WARMW00D/HUD-Audi-A4-B9-MLB-Evo-Waveshare-ESP32-S3-Touch-LCD-3.49/waveshare_hud_mockup/hud_font_fuel.c

/*******************************************************************************
 * Size: 22 px
 * Bpp: 4
 * Opts: --font Montserrat-Bold-tnum.ttf --size 22 --bpp 4 --format lvgl --symbols 0123456789.Lлgal  -o hud_font_fuel.c --force-fast-kern-format --no-prefilter
 ******************************************************************************/

#define LV_LVGL_H_INCLUDE_SIMPLE
#ifdef LV_LVGL_H_INCLUDE_SIMPLE
#include "lvgl.h"
#else
#include "lvgl/lvgl.h"
#endif

#ifndef HUD_FONT_FUEL
#define HUD_FONT_FUEL 1
#endif

#if HUD_FONT_FUEL

/*-----------------
 *    BITMAPS
 *----------------*/

/*Store the image of the glyphs*/
static LV_ATTRIBUTE_LARGE_CONST const uint8_t glyph_bitmap[] = {
    /* U+0020 " " */

    /* U+002E "." */
    0x0, 0x19, 0x0, 0x57, 0xfe, 0x80, 0x3f, 0xfc,
    0x5, 0xff, 0x70, 0x1, 0xff, 0x90, 0x0,

    /* U+0030 "0" */
    0x0, 0xc7, 0x5d, 0xfe, 0xc6, 0x0, 0xfa, 0x3f,
    0xfe, 0xd2, 0x0, 0xd1, 0xff, 0xfd, 0xa0, 0x11,
    0x7f, 0xdc, 0x80, 0x55, 0xff, 0x40, 0x2, 0x3f,
    0xe3, 0x0, 0xdb, 0xfe, 0xe0, 0x6, 0xff, 0xb4,
    0x3, 0x9b, 0xfe, 0x30, 0xff, 0xa8, 0x3, 0x93,
    0xfe, 0x50, 0xff, 0xa4, 0x3, 0x8f, 0xfe, 0x60,
    0xff, 0xa8, 0x3, 0x93, 0xfe, 0x50, 0xdf, 0xf6,
    0x80, 0x73, 0x7f, 0xc6, 0x11, 0xff, 0x18, 0x6,
    0xdf, 0xf7, 0x0, 0xb, 0xfe, 0xe4, 0x2, 0xaf,
    0xfa, 0x0, 0x28, 0xff, 0xfe, 0xd0, 0xe, 0x8f,
    0xff, 0xb4, 0x80, 0x3c, 0x75, 0xdf, 0xec, 0x60,
    0xc,

    /* U+0031 "1" */
    0xd, 0xff, 0xf0, 0x80, 0x6d, 0xff, 0xf0, 0x80,
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
    0xff, 0x40, 0x4, 0xff, 0xf0, 0xf, 0x7f, 0x94,
    0x2, 0x7f, 0xfa, 0x7f, 0xf0, 0x80, 0x4f, 0xff,
    0x67, 0xfd, 0x20, 0x19, 0xff, 0xec, 0xff, 0x48,
    0x7, 0x3f, 0xfc
};


/*---------------------
 *  GLYPH DESCRIPTION
 *--------------------*/

static const lv_font_fmt_txt_glyph_dsc_t glyph_dsc[] = {
    {.bitmap_index = 0, .adv_w = 0, .box_w = 0, .box_h = 0, .ofs_x = 0, .ofs_y = 0} /* id = 0 reserved */,
    {.bitmap_index = 0, .adv_w = 100, .box_w = 0, .box_h = 0, .ofs_x = 0, .ofs_y = 0},
    {.bitmap_index = 0, .adv_w = 92, .box_w = 6, .box_h = 5, .ofs_x = 0, .ofs_y = 0},
    {.bitmap_index = 15, .adv_w = 246, .box_w = 15, .box_h = 15, .ofs_x = 0, .ofs_y = 0},
    {.bitmap_index = 104, .adv_w = 246, .box_w = 12, .box_h = 15, .ofs_x = 2, .ofs_y = 0},
    {.bitmap_index = 166, .adv_w = 246, .box_w = 14, .box_h = 15, .ofs_x = 0, .ofs_y = 0},
    {.bitmap_index = 237, .adv_w = 246, .box_w = 13, .box_h = 15, .ofs_x = 1, .ofs_y = 0},
    {.bitmap_index = 305, .adv_w = 246, .box_w = 15, .box_h = 15, .ofs_x = 0, .ofs_y = 0},
    {.bitmap_index = 378, .adv_w = 246, .box_w = 13, .box_h = 15, .ofs_x = 1, .ofs_y = 0},
    {.bitmap_index = 448, .adv_w = 246, .box_w = 14, .box_h = 15, .ofs_x = 1, .ofs_y = 0},
    {.bitmap_index = 534, .adv_w = 246, .box_w = 14, .box_h = 15, .ofs_x = 1, .ofs_y = 0},
    {.bitmap_index = 605, .adv_w = 246, .box_w = 14, .box_h = 15, .ofs_x = 1, .ofs_y = 0},
    {.bitmap_index = 692, .adv_w = 246, .box_w = 15, .box_h = 15, .ofs_x = 0, .ofs_y = 0},
    {.bitmap_index = 782, .adv_w = 213, .box_w = 13, .box_h = 15, .ofs_x = 1, .ofs_y = 0},
    {.bitmap_index = 843, .adv_w = 217, .box_w = 13, .box_h = 12, .ofs_x = 0, .ofs_y = 0},
    {.bitmap_index = 907, .adv_w = 246, .box_w = 14, .box_h = 16, .ofs_x = 0, .ofs_y = -4},
    {.bitmap_index = 1002, .adv_w = 106, .box_w = 5, .box_h = 17, .ofs_x = 1, .ofs_y = 0},
    {.bitmap_index = 1041, .adv_w = 234, .box_w = 13, .box_h = 12, .ofs_x = 0, .ofs_y = 0}
};

/*---------------------
 *  CHARACTER MAPPING
 *--------------------*/

static const uint16_t unicode_list_0[] = {
    0x0, 0xe, 0x10, 0x11, 0x12, 0x13, 0x14, 0x15,
    0x16, 0x17, 0x18, 0x19, 0x2c, 0x41, 0x47, 0x4c,
    0x41b
};

/*Collect the unicode lists and glyph_id offsets*/
static const lv_font_fmt_txt_cmap_t cmaps[] =
{
    {
        .range_start = 32, .range_length = 1052, .glyph_id_start = 1,
        .unicode_list = unicode_list_0, .glyph_id_ofs_list = NULL, .list_length = 17, .type = LV_FONT_FMT_TXT_CMAP_SPARSE_TINY
    }
};



/*--------------------
 *  ALL CUSTOM DATA
 *--------------------*/

#if LVGL_VERSION_MAJOR == 8
/*Store all the custom data of the font*/
static  lv_font_fmt_txt_glyph_cache_t cache;
#endif

#if LVGL_VERSION_MAJOR >= 8
static const lv_font_fmt_txt_dsc_t font_dsc = {
#else
static lv_font_fmt_txt_dsc_t font_dsc = {
#endif
    .glyph_bitmap = glyph_bitmap,
    .glyph_dsc = glyph_dsc,
    .cmaps = cmaps,
    .kern_dsc = NULL,
    .kern_scale = 0,
    .cmap_num = 1,
    .bpp = 4,
    .kern_classes = 0,
    .bitmap_format = 2,
#if LVGL_VERSION_MAJOR == 8
    .cache = &cache
#endif
};



/*-----------------
 *  PUBLIC FONT
 *----------------*/

/*Initialize a public general font descriptor*/
#if LVGL_VERSION_MAJOR >= 8
const lv_font_t hud_font_fuel = {
#else
lv_font_t hud_font_fuel = {
#endif
    .get_glyph_dsc = lv_font_get_glyph_dsc_fmt_txt,    /*Function pointer to get glyph's data*/
    .get_glyph_bitmap = lv_font_get_bitmap_fmt_txt,    /*Function pointer to get glyph's bitmap*/
    .line_height = 21,          /*The maximum line height required by the font*/
    .base_line = 4,             /*Baseline measured from the bottom of the line*/
#if !(LVGL_VERSION_MAJOR == 6 && LVGL_VERSION_MINOR == 0)
    .subpx = LV_FONT_SUBPX_NONE,
#endif
#if LV_VERSION_CHECK(7, 4, 0) || LVGL_VERSION_MAJOR >= 8
    .underline_position = -2,
    .underline_thickness = 1,
#endif
    .dsc = &font_dsc,          /*The custom font data. Will be accessed by `get_glyph_bitmap/dsc` */
#if LV_VERSION_CHECK(8, 2, 0) || LVGL_VERSION_MAJOR >= 9
    .fallback = NULL,
#endif
    .user_data = NULL,
};



#endif /*#if HUD_FONT_FUEL*/
