WARMW00D/HUD-Audi-A4-B9-MLB-Evo-Waveshare-ESP32-S3-Touch-LCD-3.49/waveshare_hud_mockup/hud_font_kmh.c

/*******************************************************************************
 * Size: 38 px
 * Bpp: 4
 * Opts: --font Montserrat-Bold-tnum.ttf --size 38 --bpp 4 --format lvgl --symbols km/hpкмч -o hud_font_kmh.c --force-fast-kern-format --no-prefilter
 ******************************************************************************/

#define LV_LVGL_H_INCLUDE_SIMPLE
#ifdef LV_LVGL_H_INCLUDE_SIMPLE
#include "lvgl.h"
#else
#include "lvgl/lvgl.h"
#endif

#ifndef HUD_FONT_KMH
#define HUD_FONT_KMH 1
#endif

#if HUD_FONT_KMH

/*-----------------
 *    BITMAPS
 *----------------*/

/*Store the image of the glyphs*/
static LV_ATTRIBUTE_LARGE_CONST const uint8_t glyph_bitmap[] = {
    /* U+002F "/" */
    0x0, 0xff, 0xe0, 0xf7, 0xfe, 0x60, 0xf, 0xfe,
    0x1, 0xff, 0xf0, 0x80, 0x7f, 0xf0, 0x27, 0xff,
    0x58, 0x7, 0xff, 0x7, 0xbf, 0xf2, 0x80, 0x7f,
    0xf0, 0x13, 0xff, 0x80, 0x3f, 0xf8, 0x35, 0xff,
    0xa8, 0x3, 0xff, 0x83, 0xff, 0xc8, 0x1, 0xff,
    0xc0, 0x5f, 0xfd, 0xc0, 0x1f, 0xfc, 0x1a, 0xff,
    0xd2, 0x1, 0xff, 0xc1, 0xff, 0xe4, 0x0, 0xff,
    0xe0, 0x2f, 0xfe, 0xe0, 0xf, 0xfe, 0xd, 0xff,
    0xe8, 0x0, 0xff, 0xe0, 0xf, 0xff, 0x18, 0x7,
    0xff, 0x1, 0xbf, 0xf6, 0x80, 0x7f, 0xf0, 0x73,
    0xff, 0x40, 0x7, 0xff, 0x0, 0x7f, 0xf8, 0x80,
    0x3f, 0xf8, 0xf, 0xff, 0xb4, 0x3, 0xff, 0x83,
    0xbf, 0xf9, 0xc0, 0x3f, 0xf8, 0x5, 0xff, 0xc4,
    0x1, 0xff, 0xc0, 0x8f, 0xfd, 0x80, 0x1f, 0xfc,
    0x1d, 0xff, 0xcc, 0x1, 0xff, 0xc0, 0x3f, 0xfe,
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
    0x8f, 0xff, 0x88, 0x2, 0x3f, 0xfe, 0x22, 0x7f,
    0xf1, 0x80, 0x6a, 0xff, 0xa0, 0x3, 0x1f, 0xff,
    0x11, 0x3f, 0xf8, 0xc0, 0x31, 0x7f, 0xb8, 0x3,
    0x8f, 0xff, 0x88, 0x9f, 0xfc, 0x60, 0x1f, 0xfc,
    0x13, 0xff, 0xe2, 0x27, 0xff, 0x18, 0x7, 0xff,
    0x4, 0xff, 0xf8, 0x80,

    /* U+0447 "ч" */
    0xcf, 0xfe, 0x30, 0xf, 0xaf, 0xff, 0x8f, 0x3f,
    0xf8, 0xc0, 0x3e, 0xbf, 0xfe, 0x3c, 0xff, 0xe3,
    0x0, 0xfa, 0xff, 0xf8, 0xf3, 0xff, 0x8c, 0x3,
    0xeb, 0xff, 0xe3, 0xcf, 0xfe, 0x30, 0xf, 0xaf,
    0xff, 0x8f, 0x3f, 0xf8, 0xc0, 0x3e, 0xbf, 0xfe,
    0x3c, 0xff, 0xe3, 0x0, 0xfa, 0xff, 0xf8, 0xef,
    0xff, 0x90, 0x3, 0xeb, 0xff, 0xe3, 0x9f, 0xfe,
    0xa0, 0xf, 0xaf, 0xff, 0x8d, 0xbf, 0xfd, 0x46,
    0x0, 0x25, 0xaf, 0xff, 0x18, 0xff, 0xff, 0xf1,
    0xcc, 0x27, 0xff, 0xff, 0x8c, 0x60, 0xb, 0xff,
    0xff, 0xe2, 0x98, 0x4, 0xfd, 0xff, 0xfa, 0xb3,
    0xff, 0x8c, 0x3, 0x91, 0xe6, 0x67, 0x40, 0x5,
    0xff, 0xf1, 0x80, 0x7f, 0xf0, 0xaf, 0xff, 0x8c,
    0x3, 0xff, 0x85, 0x7f, 0xfc, 0x60, 0x1f, 0xfc,
    0x2b, 0xff, 0xe3, 0x0, 0xff, 0xe1, 0x5f, 0xff,
    0x18, 0x7, 0xff, 0xa, 0xff, 0xf8, 0xc0, 0x3f,
    0xf8, 0x57, 0xff, 0xc6
};


/*---------------------
 *  GLYPH DESCRIPTION
 *--------------------*/

static const lv_font_fmt_txt_glyph_dsc_t glyph_dsc[] = {
    {.bitmap_index = 0, .adv_w = 0, .box_w = 0, .box_h = 0, .ofs_x = 0, .ofs_y = 0} /* id = 0 reserved */,
    {.bitmap_index = 0, .adv_w = 238, .box_w = 19, .box_h = 36, .ofs_x = -2, .ofs_y = -4},
    {.bitmap_index = 200, .adv_w = 420, .box_w = 22, .box_h = 29, .ofs_x = 2, .ofs_y = 0},
    {.bitmap_index = 389, .adv_w = 398, .box_w = 24, .box_h = 29, .ofs_x = 2, .ofs_y = 0},
    {.bitmap_index = 593, .adv_w = 638, .box_w = 36, .box_h = 21, .ofs_x = 2, .ofs_y = 0},
    {.bitmap_index = 818, .adv_w = 420, .box_w = 23, .box_h = 28, .ofs_x = 2, .ofs_y = -7},
    {.bitmap_index = 1005, .adv_w = 390, .box_w = 23, .box_h = 21, .ofs_x = 2, .ofs_y = 0},
    {.bitmap_index = 1161, .adv_w = 496, .box_w = 27, .box_h = 21, .ofs_x = 2, .ofs_y = 0},
    {.bitmap_index = 1349, .adv_w = 385, .box_w = 21, .box_h = 21, .ofs_x = 1, .ofs_y = 0}
};

/*---------------------
 *  CHARACTER MAPPING
 *--------------------*/

static const uint16_t unicode_list_0[] = {
    0x0, 0x39, 0x3c, 0x3e, 0x41, 0x40b, 0x40d, 0x418
};

/*Collect the unicode lists and glyph_id offsets*/
static const lv_font_fmt_txt_cmap_t cmaps[] =
{
    {
        .range_start = 47, .range_length = 1049, .glyph_id_start = 1,
        .unicode_list = unicode_list_0, .glyph_id_ofs_list = NULL, .list_length = 8, .type = LV_FONT_FMT_TXT_CMAP_SPARSE_TINY
    }
};



/*--------------------
 *  ALL CUSTOM DATA
 *--------------------*/

#if LVGL_VERSION_MAJOR == 8
/*Store all the custom data of the font*/
static  lv_font_fmt_txt_glyph_cache_t cache;
#endif

#if LVGL_VERSION_MAJOR >= 8
static const lv_font_fmt_txt_dsc_t font_dsc = {
#else
static lv_font_fmt_txt_dsc_t font_dsc = {
#endif
    .glyph_bitmap = glyph_bitmap,
    .glyph_dsc = glyph_dsc,
    .cmaps = cmaps,
    .kern_dsc = NULL,
    .kern_scale = 0,
    .cmap_num = 1,
    .bpp = 4,
    .kern_classes = 0,
    .bitmap_format = 2,
#if LVGL_VERSION_MAJOR == 8
    .cache = &cache
#endif
};



/*-----------------
 *  PUBLIC FONT
 *----------------*/

/*Initialize a public general font descriptor*/
#if LVGL_VERSION_MAJOR >= 8
const lv_font_t hud_font_kmh = {
#else
lv_font_t hud_font_kmh = {
#endif
    .get_glyph_dsc = lv_font_get_glyph_dsc_fmt_txt,    /*Function pointer to get glyph's data*/
    .get_glyph_bitmap = lv_font_get_bitmap_fmt_txt,    /*Function pointer to get glyph's bitmap*/
    .line_height = 39,          /*The maximum line height required by the font*/
    .base_line = 7,             /*Baseline measured from the bottom of the line*/
#if !(LVGL_VERSION_MAJOR == 6 && LVGL_VERSION_MINOR == 0)
    .subpx = LV_FONT_SUBPX_NONE,
#endif
#if LV_VERSION_CHECK(7, 4, 0) || LVGL_VERSION_MAJOR >= 8
    .underline_position = -4,
    .underline_thickness = 2,
#endif
    .dsc = &font_dsc,          /*The custom font data. Will be accessed by `get_glyph_bitmap/dsc` */
#if LV_VERSION_CHECK(8, 2, 0) || LVGL_VERSION_MAJOR >= 9
    .fallback = NULL,
#endif
    .user_data = NULL,
};



#endif /*#if HUD_FONT_KMH*/
