WARMW00D/HUD-Audi-A4-B9-MLB-Evo-Waveshare-ESP32-S3-Touch-LCD-3.49/waveshare_hud_mockup/hud_font_route.c

/*******************************************************************************
 * Size: 28 px
 * Bpp: 4
 * Opts: --font Montserrat-Bold-tnum.ttf --size 28 --bpp 4 --format lvgl --symbols 0123456789:.kmhift кмч -o hud_font_route.c --force-fast-kern-format --no-prefilter
 ******************************************************************************/

#define LV_LVGL_H_INCLUDE_SIMPLE
#ifdef LV_LVGL_H_INCLUDE_SIMPLE
#include "lvgl.h"
#else
#include "lvgl/lvgl.h"
#endif

#ifndef HUD_FONT_ROUTE
#define HUD_FONT_ROUTE 1
#endif

#if HUD_FONT_ROUTE

/*-----------------
 *    BITMAPS
 *----------------*/

/*Store the image of the glyphs*/
static LV_ATTRIBUTE_LARGE_CONST const uint8_t glyph_bitmap[] = {
    /* U+0020 " " */

    /* U+002E "." */
    0x0, 0xa, 0x18, 0x4, 0xbf, 0xf5, 0x0, 0x3b,
    0xff, 0x20, 0x7f, 0xf2, 0x86, 0x7f, 0xe2, 0x1,
    0xbf, 0xd5, 0x0,

    /* U+0030 "0" */
    0x0, 0xe6, 0xbe, 0xff, 0x6c, 0x98, 0x7, 0xe3,
    0xdf, 0xff, 0xd4, 0x20, 0x1c, 0x9f, 0xff, 0xf6,
    0x88, 0x4, 0x5f, 0xfe, 0xcd, 0xff, 0xea, 0x0,
    0xab, 0xff, 0x48, 0x4, 0x7b, 0xff, 0x90, 0x7,
    0xff, 0x60, 0x7, 0x17, 0xfe, 0xb0, 0x6f, 0xfc,
    0x80, 0x1e, 0xaf, 0xfc, 0x13, 0xff, 0x80, 0x3e,
    0x6f, 0xfc, 0x77, 0xff, 0x70, 0x7, 0xc9, 0xff,
    0x92, 0xff, 0xed, 0x0, 0xf9, 0x3f, 0xf2, 0xdf,
    0xfd, 0xc0, 0x1f, 0x27, 0xfe, 0x49, 0xff, 0xc0,
    0x1f, 0x37, 0xfe, 0x36, 0xff, 0xc8, 0x1, 0xea,
    0xff, 0xc0, 0x3f, 0xfb, 0x0, 0x38, 0xbf, 0xf5,
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
    0xeb, 0xef, 0xf8, 0x0, 0xbf, 0xfc, 0x40, 0x7f,
    0xf5, 0xf7, 0xfc, 0x1, 0x67, 0xfd, 0x0, 0x3,
    0xff, 0xaf, 0xbf, 0xe0, 0x8, 0xff, 0xdc, 0x1,
    0x1f, 0xfd, 0x7d, 0xff, 0x0, 0x66, 0x94, 0x0,
    0x8f, 0xfe, 0xbe, 0xff, 0x80, 0x3f, 0xc7, 0xff,
    0x60,

    /* U+0447 "ч" */
    0x1f, 0xfc, 0x80, 0x1d, 0x7f, 0xf5, 0xf, 0xfe,
    0x40, 0xe, 0xbf, 0xfa, 0x87, 0xff, 0x20, 0x7,
    0x5f, 0xfd, 0x43, 0xff, 0x90, 0x3, 0xaf, 0xfe,
    0xa1, 0xff, 0xc8, 0x1, 0xd7, 0xff, 0x50, 0x7f,
    0xe7, 0x0, 0xeb, 0xff, 0xa8, 0x3b, 0xff, 0x28,
    0x0, 0x9b, 0xbf, 0xea, 0x8, 0xff, 0xff, 0xe0,
    0xd0, 0xe, 0xff, 0xff, 0xf0, 0x28, 0x0, 0x33,
    0xff, 0xea, 0xdf, 0xfa, 0x80, 0x38, 0x91, 0x6,
    0x0, 0xbf, 0xfa, 0x80, 0x3f, 0xeb, 0xff, 0xa8,
    0x3, 0xfe, 0xbf, 0xfa, 0x80, 0x3f, 0xeb, 0xff,
    0xa8, 0x3, 0xfe, 0xbf, 0xfa, 0x80
};


/*---------------------
 *  GLYPH DESCRIPTION
 *--------------------*/

static const lv_font_fmt_txt_glyph_dsc_t glyph_dsc[] = {
    {.bitmap_index = 0, .adv_w = 0, .box_w = 0, .box_h = 0, .ofs_x = 0, .ofs_y = 0} /* id = 0 reserved */,
    {.bitmap_index = 0, .adv_w = 127, .box_w = 0, .box_h = 0, .ofs_x = 0, .ofs_y = 0},
    {.bitmap_index = 0, .adv_w = 117, .box_w = 7, .box_h = 6, .ofs_x = 0, .ofs_y = 0},
    {.bitmap_index = 19, .adv_w = 314, .box_w = 18, .box_h = 19, .ofs_x = 1, .ofs_y = 0},
    {.bitmap_index = 139, .adv_w = 314, .box_w = 14, .box_h = 19, .ofs_x = 3, .ofs_y = 0},
    {.bitmap_index = 222, .adv_w = 314, .box_w = 17, .box_h = 19, .ofs_x = 1, .ofs_y = 0},
    {.bitmap_index = 323, .adv_w = 314, .box_w = 17, .box_h = 19, .ofs_x = 1, .ofs_y = 0},
    {.bitmap_index = 427, .adv_w = 314, .box_w = 18, .box_h = 19, .ofs_x = 1, .ofs_y = 0},
    {.bitmap_index = 531, .adv_w = 314, .box_w = 17, .box_h = 19, .ofs_x = 1, .ofs_y = 0},
    {.bitmap_index = 638, .adv_w = 314, .box_w = 18, .box_h = 19, .ofs_x = 1, .ofs_y = 0},
    {.bitmap_index = 759, .adv_w = 314, .box_w = 18, .box_h = 19, .ofs_x = 1, .ofs_y = 0},
    {.bitmap_index = 863, .adv_w = 314, .box_w = 18, .box_h = 19, .ofs_x = 1, .ofs_y = 0},
    {.bitmap_index = 988, .adv_w = 314, .box_w = 18, .box_h = 19, .ofs_x = 1, .ofs_y = 0},
    {.bitmap_index = 1108, .adv_w = 117, .box_w = 7, .box_h = 15, .ofs_x = 0, .ofs_y = 0},
    {.bitmap_index = 1146, .adv_w = 173, .box_w = 12, .box_h = 21, .ofs_x = 0, .ofs_y = 0},
    {.bitmap_index = 1233, .adv_w = 310, .box_w = 16, .box_h = 21, .ofs_x = 2, .ofs_y = 0},
    {.bitmap_index = 1340, .adv_w = 135, .box_w = 6, .box_h = 22, .ofs_x = 1, .ofs_y = 0},
    {.bitmap_index = 1392, .adv_w = 293, .box_w = 17, .box_h = 21, .ofs_x = 2, .ofs_y = 0},
    {.bitmap_index = 1513, .adv_w = 470, .box_w = 26, .box_h = 15, .ofs_x = 2, .ofs_y = 0},
    {.bitmap_index = 1651, .adv_w = 195, .box_w = 12, .box_h = 19, .ofs_x = 0, .ofs_y = 0},
    {.bitmap_index = 1731, .adv_w = 288, .box_w = 16, .box_h = 15, .ofs_x = 2, .ofs_y = 0},
    {.bitmap_index = 1826, .adv_w = 365, .box_w = 19, .box_h = 15, .ofs_x = 2, .ofs_y = 0},
    {.bitmap_index = 1939, .adv_w = 284, .box_w = 16, .box_h = 15, .ofs_x = 0, .ofs_y = 0}
};

/*---------------------
 *  CHARACTER MAPPING
 *--------------------*/

static const uint16_t unicode_list_0[] = {
    0x0, 0xe, 0x10, 0x11, 0x12, 0x13, 0x14, 0x15,
    0x16, 0x17, 0x18, 0x19, 0x1a, 0x46, 0x48, 0x49,
    0x4b, 0x4d, 0x54, 0x41a, 0x41c, 0x427
};

/*Collect the unicode lists and glyph_id offsets*/
static const lv_font_fmt_txt_cmap_t cmaps[] =
{
    {
        .range_start = 32, .range_length = 1064, .glyph_id_start = 1,
        .unicode_list = unicode_list_0, .glyph_id_ofs_list = NULL, .list_length = 22, .type = LV_FONT_FMT_TXT_CMAP_SPARSE_TINY
    }
};



/*--------------------
 *  ALL CUSTOM DATA
 *--------------------*/

#if LVGL_VERSION_MAJOR == 8
/*Store all the custom data of the font*/
static  lv_font_fmt_txt_glyph_cache_t cache;
#endif

#if LVGL_VERSION_MAJOR >= 8
static const lv_font_fmt_txt_dsc_t font_dsc = {
#else
static lv_font_fmt_txt_dsc_t font_dsc = {
#endif
    .glyph_bitmap = glyph_bitmap,
    .glyph_dsc = glyph_dsc,
    .cmaps = cmaps,
    .kern_dsc = NULL,
    .kern_scale = 0,
    .cmap_num = 1,
    .bpp = 4,
    .kern_classes = 0,
    .bitmap_format = 2,
#if LVGL_VERSION_MAJOR == 8
    .cache = &cache
#endif
};



/*-----------------
 *  PUBLIC FONT
 *----------------*/

/*Initialize a public general font descriptor*/
#if LVGL_VERSION_MAJOR >= 8
const lv_font_t hud_font_route = {
#else
lv_font_t hud_font_route = {
#endif
    .get_glyph_dsc = lv_font_get_glyph_dsc_fmt_txt,    /*Function pointer to get glyph's data*/
    .get_glyph_bitmap = lv_font_get_bitmap_fmt_txt,    /*Function pointer to get glyph's bitmap*/
    .line_height = 22,          /*The maximum line height required by the font*/
    .base_line = 0,             /*Baseline measured from the bottom of the line*/
#if !(LVGL_VERSION_MAJOR == 6 && LVGL_VERSION_MINOR == 0)
    .subpx = LV_FONT_SUBPX_NONE,
#endif
#if LV_VERSION_CHECK(7, 4, 0) || LVGL_VERSION_MAJOR >= 8
    .underline_position = -3,
    .underline_thickness = 1,
#endif
    .dsc = &font_dsc,          /*The custom font data. Will be accessed by `get_glyph_bitmap/dsc` */
#if LV_VERSION_CHECK(8, 2, 0) || LVGL_VERSION_MAJOR >= 9
    .fallback = NULL,
#endif
    .user_data = NULL,
};



#endif /*#if HUD_FONT_ROUTE*/
