WARMW00D/HUD-Audi-A4-B9-MLB-Evo-Waveshare-ESP32-S3-Touch-LCD-3.49/waveshare_hud_mockup/hud_font_sign2.c

/*******************************************************************************
 * Size: 40 px
 * Bpp: 4
 * Opts: --font RobotoCondensed-Bold.ttf --size 40 --bpp 4 --format lvgl --symbols 0123456789 -o hud_font_sign2.c --force-fast-kern-format --no-prefilter
 ******************************************************************************/

#define LV_LVGL_H_INCLUDE_SIMPLE
#ifdef LV_LVGL_H_INCLUDE_SIMPLE
#include "lvgl.h"
#else
#include "lvgl/lvgl.h"
#endif

#ifndef HUD_FONT_SIGN2
#define HUD_FONT_SIGN2 1
#endif

#if HUD_FONT_SIGN2

/*-----------------
 *    BITMAPS
 *----------------*/

/*Store the image of the glyphs*/
static LV_ATTRIBUTE_LARGE_CONST const uint8_t glyph_bitmap[] = {
    /* U+0030 "0" */
    0x0, 0xe2, 0x9d, 0xff, 0x75, 0x20, 0x7, 0xf4,
    0x7f, 0xfe, 0xb0, 0xf, 0xa3, 0xff, 0xfd, 0x80,
    0x1c, 0x9f, 0xff, 0xfc, 0x7, 0x0, 0xd9, 0xff,
    0xd9, 0x7f, 0xfe, 0x10, 0x1, 0x7f, 0xf3, 0x80,
    0x13, 0xff, 0x98, 0x1, 0x1f, 0xfb, 0x80, 0x35,
    0xff, 0xeb, 0x0, 0x5f, 0xfe, 0xa0, 0xc, 0xff,
    0xfc, 0x0, 0xef, 0xfc, 0xe0, 0x19, 0x3f, 0xf8,
    0x83, 0xff, 0x98, 0x3, 0x17, 0xff, 0x18, 0xff,
    0xf2, 0x80, 0x62, 0xff, 0xe5, 0x2f, 0xfe, 0x50,
    0xc, 0x5f, 0xfc, 0xa5, 0xff, 0xca, 0x1, 0x8b,
    0xff, 0x94, 0xbf, 0xf9, 0x40, 0x31, 0x7f, 0xf2,
    0x97, 0xff, 0x28, 0x6, 0x2f, 0xfe, 0x52, 0xff,
    0xe5, 0x0, 0xc5, 0xff, 0xca, 0x5f, 0xfc, 0xa0,
    0x18, 0xbf, 0xf9, 0x4b, 0xff, 0x94, 0x3, 0x17,
    0xff, 0x28, 0xff, 0xf2, 0x80, 0x62, 0xff, 0xe5,
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
    0xff, 0xe6, 0x0, 0xfe, 0x3a, 0xff, 0xed, 0x0,
    0xfa, 0x37, 0xff, 0xf1, 0x80, 0x7d, 0x3f, 0xff,
    0x98, 0x3, 0xf4, 0xff, 0xfc, 0xc0, 0x1f, 0xd3,
    0xff, 0xd6, 0x40, 0x1f, 0xe9, 0xfe, 0xb8, 0x20,
    0xf, 0xc0
};


/*---------------------
 *  GLYPH DESCRIPTION
 *--------------------*/

static const lv_font_fmt_txt_glyph_dsc_t glyph_dsc[] = {
    {.bitmap_index = 0, .adv_w = 0, .box_w = 0, .box_h = 0, .ofs_x = 0, .ofs_y = 0} /* id = 0 reserved */,
    {.bitmap_index = 0, .adv_w = 323, .box_w = 18, .box_h = 29, .ofs_x = 1, .ofs_y = 0},
    {.bitmap_index = 183, .adv_w = 323, .box_w = 11, .box_h = 29, .ofs_x = 3, .ofs_y = 0},
    {.bitmap_index = 285, .adv_w = 323, .box_w = 18, .box_h = 29, .ofs_x = 1, .ofs_y = 0},
    {.bitmap_index = 438, .adv_w = 323, .box_w = 18, .box_h = 29, .ofs_x = 1, .ofs_y = 0},
    {.bitmap_index = 606, .adv_w = 323, .box_w = 18, .box_h = 29, .ofs_x = 1, .ofs_y = 0},
    {.bitmap_index = 763, .adv_w = 323, .box_w = 18, .box_h = 29, .ofs_x = 1, .ofs_y = 0},
    {.bitmap_index = 931, .adv_w = 323, .box_w = 18, .box_h = 29, .ofs_x = 1, .ofs_y = 0},
    {.bitmap_index = 1101, .adv_w = 323, .box_w = 18, .box_h = 29, .ofs_x = 1, .ofs_y = 0},
    {.bitmap_index = 1241, .adv_w = 323, .box_w = 18, .box_h = 29, .ofs_x = 1, .ofs_y = 0},
    {.bitmap_index = 1425, .adv_w = 323, .box_w = 18, .box_h = 29, .ofs_x = 1, .ofs_y = 0}
};

/*---------------------
 *  CHARACTER MAPPING
 *--------------------*/



/*Collect the unicode lists and glyph_id offsets*/
static const lv_font_fmt_txt_cmap_t cmaps[] =
{
    {
        .range_start = 48, .range_length = 10, .glyph_id_start = 1,
        .unicode_list = NULL, .glyph_id_ofs_list = NULL, .list_length = 0, .type = LV_FONT_FMT_TXT_CMAP_FORMAT0_TINY
    }
};



/*--------------------
 *  ALL CUSTOM DATA
 *--------------------*/

#if LVGL_VERSION_MAJOR == 8
/*Store all the custom data of the font*/
static  lv_font_fmt_txt_glyph_cache_t cache;
#endif

#if LVGL_VERSION_MAJOR >= 8
static const lv_font_fmt_txt_dsc_t font_dsc = {
#else
static lv_font_fmt_txt_dsc_t font_dsc = {
#endif
    .glyph_bitmap = glyph_bitmap,
    .glyph_dsc = glyph_dsc,
    .cmaps = cmaps,
    .kern_dsc = NULL,
    .kern_scale = 0,
    .cmap_num = 1,
    .bpp = 4,
    .kern_classes = 0,
    .bitmap_format = 2,
#if LVGL_VERSION_MAJOR == 8
    .cache = &cache
#endif
};



/*-----------------
 *  PUBLIC FONT
 *----------------*/

/*Initialize a public general font descriptor*/
#if LVGL_VERSION_MAJOR >= 8
const lv_font_t hud_font_sign2 = {
#else
lv_font_t hud_font_sign2 = {
#endif
    .get_glyph_dsc = lv_font_get_glyph_dsc_fmt_txt,    /*Function pointer to get glyph's data*/
    .get_glyph_bitmap = lv_font_get_bitmap_fmt_txt,    /*Function pointer to get glyph's bitmap*/
    .line_height = 29,          /*The maximum line height required by the font*/
    .base_line = 0,             /*Baseline measured from the bottom of the line*/
#if !(LVGL_VERSION_MAJOR == 6 && LVGL_VERSION_MINOR == 0)
    .subpx = LV_FONT_SUBPX_NONE,
#endif
#if LV_VERSION_CHECK(7, 4, 0) || LVGL_VERSION_MAJOR >= 8
    .underline_position = -3,
    .underline_thickness = 2,
#endif
    .dsc = &font_dsc,          /*The custom font data. Will be accessed by `get_glyph_bitmap/dsc` */
#if LV_VERSION_CHECK(8, 2, 0) || LVGL_VERSION_MAJOR >= 9
    .fallback = NULL,
#endif
    .user_data = NULL,
};



#endif /*#if HUD_FONT_SIGN2*/
