WARMW00D/HUD-Audi-A4-B9-MLB-Evo-Waveshare-ESP32-S3-Touch-LCD-3.49/waveshare_hud_mockup/hud_font_sign3.c

/*******************************************************************************
 * Size: 30 px
 * Bpp: 4
 * Opts: --font RobotoCondensed-Bold.ttf --size 30 --bpp 4 --format lvgl --symbols 0123456789 -o hud_font_sign3.c --force-fast-kern-format --no-prefilter
 ******************************************************************************/

#define LV_LVGL_H_INCLUDE_SIMPLE
#ifdef LV_LVGL_H_INCLUDE_SIMPLE
#include "lvgl.h"
#else
#include "lvgl/lvgl.h"
#endif

#ifndef HUD_FONT_SIGN3
#define HUD_FONT_SIGN3 1
#endif

#if HUD_FONT_SIGN3

/*-----------------
 *    BITMAPS
 *----------------*/

/*Store the image of the glyphs*/
static LV_ATTRIBUTE_LARGE_CONST const uint8_t glyph_bitmap[] = {
    /* U+0030 "0" */
    0x0, 0x8a, 0xbb, 0xfa, 0xd0, 0x3, 0x97, 0xff,
    0xe8, 0x0, 0x8b, 0xff, 0xf9, 0x40, 0x17, 0xff,
    0x63, 0x5f, 0xfd, 0xa0, 0x3f, 0xf8, 0x40, 0x1d,
    0xff, 0x1a, 0xff, 0xd6, 0x1, 0x4f, 0xfc, 0xee,
    0xff, 0xa4, 0x2, 0x6f, 0xfa, 0xa7, 0xfe, 0x80,
    0x9, 0x7f, 0xeb, 0x9f, 0xfa, 0x0, 0x25, 0xff,
    0xb2, 0x7f, 0xe8, 0x0, 0x97, 0xfe, 0xc9, 0xff,
    0xa0, 0x2, 0x5f, 0xfb, 0x27, 0xfe, 0x80, 0x9,
    0x7f, 0xec, 0x9f, 0xfa, 0x0, 0x25, 0xff, 0xb2,
    0x7f, 0xe8, 0x0, 0x97, 0xfe, 0xb7, 0xff, 0xa4,
    0x2, 0x6f, 0xfa, 0x97, 0xfe, 0xc0, 0xa, 0x7f,
    0xe7, 0x1f, 0xfc, 0x20, 0xe, 0xff, 0x8c, 0x2f,
    0xfe, 0xc6, 0xbf, 0xfb, 0x40, 0x5, 0xff, 0xfc,
    0xa0, 0x12, 0xff, 0xfd, 0x0, 0x1c, 0x55, 0xdf,
    0xd6, 0x80, 0x10,

    /* U+0031 "1" */
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
    0xff, 0x18, 0x7, 0xee, 0xff, 0x80, 0x3f, 0x37,
    0xfd, 0x40, 0x1f, 0x2f, 0xfe, 0x30, 0xd, 0x13,
    0xbf, 0xfa, 0x40, 0x3b, 0xff, 0xd6, 0x1, 0xef,
    0xfe, 0x90, 0xf, 0xbf, 0xb2, 0x8, 0x3, 0x80
};


/*---------------------
 *  GLYPH DESCRIPTION
 *--------------------*/

static const lv_font_fmt_txt_glyph_dsc_t glyph_dsc[] = {
    {.bitmap_index = 0, .adv_w = 0, .box_w = 0, .box_h = 0, .ofs_x = 0, .ofs_y = 0} /* id = 0 reserved */,
    {.bitmap_index = 0, .adv_w = 243, .box_w = 13, .box_h = 21, .ofs_x = 1, .ofs_y = 0},
    {.bitmap_index = 115, .adv_w = 243, .box_w = 9, .box_h = 21, .ofs_x = 2, .ofs_y = 0},
    {.bitmap_index = 191, .adv_w = 243, .box_w = 13, .box_h = 21, .ofs_x = 1, .ofs_y = 0},
    {.bitmap_index = 285, .adv_w = 243, .box_w = 13, .box_h = 21, .ofs_x = 1, .ofs_y = 0},
    {.bitmap_index = 387, .adv_w = 243, .box_w = 15, .box_h = 21, .ofs_x = 0, .ofs_y = 0},
    {.bitmap_index = 495, .adv_w = 243, .box_w = 13, .box_h = 21, .ofs_x = 1, .ofs_y = 0},
    {.bitmap_index = 592, .adv_w = 243, .box_w = 14, .box_h = 21, .ofs_x = 1, .ofs_y = 0},
    {.bitmap_index = 704, .adv_w = 243, .box_w = 13, .box_h = 21, .ofs_x = 1, .ofs_y = 0},
    {.bitmap_index = 789, .adv_w = 243, .box_w = 13, .box_h = 21, .ofs_x = 1, .ofs_y = 0},
    {.bitmap_index = 900, .adv_w = 243, .box_w = 13, .box_h = 21, .ofs_x = 1, .ofs_y = 0}
};

/*---------------------
 *  CHARACTER MAPPING
 *--------------------*/



/*Collect the unicode lists and glyph_id offsets*/
static const lv_font_fmt_txt_cmap_t cmaps[] =
{
    {
        .range_start = 48, .range_length = 10, .glyph_id_start = 1,
        .unicode_list = NULL, .glyph_id_ofs_list = NULL, .list_length = 0, .type = LV_FONT_FMT_TXT_CMAP_FORMAT0_TINY
    }
};



/*--------------------
 *  ALL CUSTOM DATA
 *--------------------*/

#if LVGL_VERSION_MAJOR == 8
/*Store all the custom data of the font*/
static  lv_font_fmt_txt_glyph_cache_t cache;
#endif

#if LVGL_VERSION_MAJOR >= 8
static const lv_font_fmt_txt_dsc_t font_dsc = {
#else
static lv_font_fmt_txt_dsc_t font_dsc = {
#endif
    .glyph_bitmap = glyph_bitmap,
    .glyph_dsc = glyph_dsc,
    .cmaps = cmaps,
    .kern_dsc = NULL,
    .kern_scale = 0,
    .cmap_num = 1,
    .bpp = 4,
    .kern_classes = 0,
    .bitmap_format = 2,
#if LVGL_VERSION_MAJOR == 8
    .cache = &cache
#endif
};



/*-----------------
 *  PUBLIC FONT
 *----------------*/

/*Initialize a public general font descriptor*/
#if LVGL_VERSION_MAJOR >= 8
const lv_font_t hud_font_sign3 = {
#else
lv_font_t hud_font_sign3 = {
#endif
    .get_glyph_dsc = lv_font_get_glyph_dsc_fmt_txt,    /*Function pointer to get glyph's data*/
    .get_glyph_bitmap = lv_font_get_bitmap_fmt_txt,    /*Function pointer to get glyph's bitmap*/
    .line_height = 21,          /*The maximum line height required by the font*/
    .base_line = 0,             /*Baseline measured from the bottom of the line*/
#if !(LVGL_VERSION_MAJOR == 6 && LVGL_VERSION_MINOR == 0)
    .subpx = LV_FONT_SUBPX_NONE,
#endif
#if LV_VERSION_CHECK(7, 4, 0) || LVGL_VERSION_MAJOR >= 8
    .underline_position = -2,
    .underline_thickness = 1,
#endif
    .dsc = &font_dsc,          /*The custom font data. Will be accessed by `get_glyph_bitmap/dsc` */
#if LV_VERSION_CHECK(8, 2, 0) || LVGL_VERSION_MAJOR >= 9
    .fallback = NULL,
#endif
    .user_data = NULL,
};



#endif /*#if HUD_FONT_SIGN3*/
