WARMW00D/HUD-Audi-A4-B9-MLB-Evo-Waveshare-ESP32-S3-Touch-LCD-3.49/waveshare_hud_mockup/hud_font_small.c

/*******************************************************************************
 * Size: 26 px
 * Bpp: 4
 * Opts: --font Montserrat-Bold-tnum.ttf --size 26 --bpp 4 --format lvgl --symbols 0123456789 -o hud_font_small.c --force-fast-kern-format --no-prefilter
 ******************************************************************************/

#define LV_LVGL_H_INCLUDE_SIMPLE
#ifdef LV_LVGL_H_INCLUDE_SIMPLE
#include "lvgl.h"
#else
#include "lvgl/lvgl.h"
#endif

#ifndef HUD_FONT_SMALL
#define HUD_FONT_SMALL 1
#endif

#if HUD_FONT_SMALL

/*-----------------
 *    BITMAPS
 *----------------*/

/*Store the image of the glyphs*/
static LV_ATTRIBUTE_LARGE_CONST const uint8_t glyph_bitmap[] = {
    /* U+0030 "0" */
    0x0, 0xc7, 0x3b, 0xfe, 0xea, 0x40, 0xf, 0xd1,
    0xff, 0xfa, 0xc0, 0x3d, 0x5f, 0xff, 0xec, 0x0,
    0xcd, 0xff, 0xba, 0x63, 0x7f, 0xf4, 0x80, 0x5d,
    0xff, 0x58, 0x6, 0x9f, 0xfc, 0x40, 0xbf, 0xf8,
    0x40, 0x3b, 0x7f, 0xe8, 0x9, 0xff, 0xac, 0x3,
    0xd1, 0xff, 0x60, 0x5f, 0xfd, 0x0, 0x1e, 0x5f,
    0xfc, 0x1b, 0xff, 0x38, 0x7, 0x93, 0xff, 0x6,
    0xff, 0xce, 0x1, 0xe4, 0xff, 0xc1, 0x7f, 0xf4,
    0x0, 0x79, 0x7f, 0xf0, 0x4f, 0xfd, 0x60, 0x1e,
    0x8f, 0xfb, 0x1, 0x7f, 0xf0, 0x80, 0x76, 0xff,
    0xd0, 0x0, 0xef, 0xfa, 0xc0, 0x34, 0xff, 0xe2,
    0x0, 0x37, 0xfe, 0xe9, 0x8d, 0xff, 0xd2, 0x1,
    0xab, 0xff, 0xfd, 0x80, 0x1e, 0x8f, 0xff, 0xd6,
    0x1, 0xf8, 0xe7, 0x7f, 0xdd, 0x48, 0x1, 0xc0,

    /* U+0031 "1" */
    0x3f, 0xff, 0xb8, 0x3, 0x1f, 0xff, 0xdc, 0x1,
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
    0xff, 0xc2, 0x0, 0x20, 0xf, 0x37, 0xfe, 0x90,
    0x0, 0xfe, 0x43, 0x32, 0x37, 0xff, 0x68, 0x5,
    0x1f, 0xff, 0xed, 0x20, 0xb, 0xbf, 0xff, 0xa4,
    0x40, 0x31, 0x46, 0x77, 0xfb, 0xad, 0xc8, 0x3,
    0x80
};


/*---------------------
 *  GLYPH DESCRIPTION
 *--------------------*/

static const lv_font_fmt_txt_glyph_dsc_t glyph_dsc[] = {
    {.bitmap_index = 0, .adv_w = 0, .box_w = 0, .box_h = 0, .ofs_x = 0, .ofs_y = 0} /* id = 0 reserved */,
    {.bitmap_index = 0, .adv_w = 291, .box_w = 17, .box_h = 18, .ofs_x = 1, .ofs_y = 0},
    {.bitmap_index = 112, .adv_w = 291, .box_w = 13, .box_h = 18, .ofs_x = 3, .ofs_y = 0},
    {.bitmap_index = 187, .adv_w = 291, .box_w = 16, .box_h = 18, .ofs_x = 1, .ofs_y = 0},
    {.bitmap_index = 279, .adv_w = 291, .box_w = 16, .box_h = 18, .ofs_x = 1, .ofs_y = 0},
    {.bitmap_index = 369, .adv_w = 291, .box_w = 17, .box_h = 18, .ofs_x = 0, .ofs_y = 0},
    {.bitmap_index = 464, .adv_w = 291, .box_w = 16, .box_h = 18, .ofs_x = 1, .ofs_y = 0},
    {.bitmap_index = 557, .adv_w = 291, .box_w = 17, .box_h = 18, .ofs_x = 1, .ofs_y = 0},
    {.bitmap_index = 667, .adv_w = 291, .box_w = 16, .box_h = 18, .ofs_x = 1, .ofs_y = 0},
    {.bitmap_index = 755, .adv_w = 291, .box_w = 16, .box_h = 18, .ofs_x = 1, .ofs_y = 0},
    {.bitmap_index = 865, .adv_w = 291, .box_w = 16, .box_h = 18, .ofs_x = 1, .ofs_y = 0}
};

/*---------------------
 *  CHARACTER MAPPING
 *--------------------*/



/*Collect the unicode lists and glyph_id offsets*/
static const lv_font_fmt_txt_cmap_t cmaps[] =
{
    {
        .range_start = 48, .range_length = 10, .glyph_id_start = 1,
        .unicode_list = NULL, .glyph_id_ofs_list = NULL, .list_length = 0, .type = LV_FONT_FMT_TXT_CMAP_FORMAT0_TINY
    }
};



/*--------------------
 *  ALL CUSTOM DATA
 *--------------------*/

#if LVGL_VERSION_MAJOR == 8
/*Store all the custom data of the font*/
static  lv_font_fmt_txt_glyph_cache_t cache;
#endif

#if LVGL_VERSION_MAJOR >= 8
static const lv_font_fmt_txt_dsc_t font_dsc = {
#else
static lv_font_fmt_txt_dsc_t font_dsc = {
#endif
    .glyph_bitmap = glyph_bitmap,
    .glyph_dsc = glyph_dsc,
    .cmaps = cmaps,
    .kern_dsc = NULL,
    .kern_scale = 0,
    .cmap_num = 1,
    .bpp = 4,
    .kern_classes = 0,
    .bitmap_format = 2,
#if LVGL_VERSION_MAJOR == 8
    .cache = &cache
#endif
};



/*-----------------
 *  PUBLIC FONT
 *----------------*/

/*Initialize a public general font descriptor*/
#if LVGL_VERSION_MAJOR >= 8
const lv_font_t hud_font_small = {
#else
lv_font_t hud_font_small = {
#endif
    .get_glyph_dsc = lv_font_get_glyph_dsc_fmt_txt,    /*Function pointer to get glyph's data*/
    .get_glyph_bitmap = lv_font_get_bitmap_fmt_txt,    /*Function pointer to get glyph's bitmap*/
    .line_height = 18,          /*The maximum line height required by the font*/
    .base_line = 0,             /*Baseline measured from the bottom of the line*/
#if !(LVGL_VERSION_MAJOR == 6 && LVGL_VERSION_MINOR == 0)
    .subpx = LV_FONT_SUBPX_NONE,
#endif
#if LV_VERSION_CHECK(7, 4, 0) || LVGL_VERSION_MAJOR >= 8
    .underline_position = -3,
    .underline_thickness = 1,
#endif
    .dsc = &font_dsc,          /*The custom font data. Will be accessed by `get_glyph_bitmap/dsc` */
#if LV_VERSION_CHECK(8, 2, 0) || LVGL_VERSION_MAJOR >= 9
    .fallback = NULL,
#endif
    .user_data = NULL,
};



#endif /*#if HUD_FONT_SMALL*/
