WARMW00D/HUD-Audi-A4-B9-MLB-Evo-Waveshare-ESP32-S3-Touch-LCD-3.49/waveshare_hud_mockup/hud_font_speed.c

/*******************************************************************************
 * Size: 116 px
 * Bpp: 4
 * Opts: --font Montserrat-Bold-tnum.ttf --size 116 --bpp 4 --format lvgl --symbols 0123456789 -o hud_font_speed.c --force-fast-kern-format --no-prefilter
 ******************************************************************************/

#define LV_LVGL_H_INCLUDE_SIMPLE
#ifdef LV_LVGL_H_INCLUDE_SIMPLE
#include "lvgl.h"
#else
#include "lvgl/lvgl.h"
#endif

#ifndef HUD_FONT_SPEED
#define HUD_FONT_SPEED 1
#endif

#if HUD_FONT_SPEED

/*-----------------
 *    BITMAPS
 *----------------*/

/*Store the image of the glyphs*/
static LV_ATTRIBUTE_LARGE_CONST const uint8_t glyph_bitmap[] = {
    /* U+0030 "0" */
    0x0, 0xff, 0xe8, 0x12, 0xbc, 0xd5, 0xe6, 0x57,
    0x69, 0x75, 0x20, 0xf, 0xff, 0x41, 0x35, 0xf7,
    0xff, 0xff, 0x13, 0x1c, 0x80, 0x3f, 0xfc, 0x4d,
    0x9f, 0xff, 0xfc, 0xbd, 0x71, 0x0, 0xff, 0xee,
    0xc, 0x77, 0xff, 0xff, 0x42, 0x48, 0x3, 0xff,
    0xb2, 0xff, 0xff, 0xfd, 0x59, 0x10, 0xf, 0xfe,
    0xa9, 0xef, 0xff, 0xff, 0x5f, 0x94, 0x3, 0xff,
    0xa7, 0x1f, 0xff, 0xfd, 0xba, 0x0, 0xff, 0xe8,
    0xd, 0xff, 0xff, 0xf7, 0x74, 0x80, 0x3f, 0xf9,
    0xa3, 0xbf, 0xff, 0xfd, 0xfe, 0x30, 0xf, 0xfe,
    0x59, 0x77, 0xff, 0xff, 0x89, 0x0, 0x3f, 0xf9,
    0x23, 0xdf, 0xff, 0xfe, 0x43, 0x0, 0xff, 0xe3,
    0x8e, 0xff, 0xff, 0xf9, 0x88, 0x3, 0xff, 0x8d,
    0x7f, 0xff, 0xfe, 0x7d, 0x10, 0xf, 0xfe, 0x24,
    0x7f, 0xff, 0xfa, 0x6c, 0x3, 0xff, 0x86, 0x7f,
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
    0x0, 0xff, 0xe8, 0xa7, 0xff, 0xff, 0x1d, 0xc0,
    0x19, 0xff, 0xff, 0xc6, 0x0, 0xff, 0xe8, 0xaf,
    0xff, 0xff, 0x1e, 0xc0, 0x19, 0xff, 0xff, 0xc6,
    0x20, 0xf, 0xfe, 0x83, 0xff, 0xff, 0xf2, 0x0,
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
};


/*---------------------
 *  GLYPH DESCRIPTION
 *--------------------*/

static const lv_font_fmt_txt_glyph_dsc_t glyph_dsc[] = {
    {.bitmap_index = 0, .adv_w = 0, .box_w = 0, .box_h = 0, .ofs_x = 0, .ofs_y = 0} /* id = 0 reserved */,
    {.bitmap_index = 0, .adv_w = 1299, .box_w = 71, .box_h = 84, .ofs_x = 5, .ofs_y = -1},
    {.bitmap_index = 902, .adv_w = 1299, .box_w = 55, .box_h = 81, .ofs_x = 15, .ofs_y = 0},
    {.bitmap_index = 1445, .adv_w = 1299, .box_w = 67, .box_h = 82, .ofs_x = 5, .ofs_y = 0},
    {.bitmap_index = 2084, .adv_w = 1299, .box_w = 69, .box_h = 82, .ofs_x = 5, .ofs_y = -1},
    {.bitmap_index = 2725, .adv_w = 1299, .box_w = 72, .box_h = 81, .ofs_x = 4, .ofs_y = 0},
    {.bitmap_index = 3374, .adv_w = 1299, .box_w = 68, .box_h = 82, .ofs_x = 5, .ofs_y = -1},
    {.bitmap_index = 4027, .adv_w = 1299, .box_w = 70, .box_h = 84, .ofs_x = 6, .ofs_y = -1},
    {.bitmap_index = 4872, .adv_w = 1299, .box_w = 68, .box_h = 82, .ofs_x = 7, .ofs_y = 0},
    {.bitmap_index = 5488, .adv_w = 1299, .box_w = 71, .box_h = 84, .ofs_x = 5, .ofs_y = -1},
    {.bitmap_index = 6379, .adv_w = 1299, .box_w = 71, .box_h = 84, .ofs_x = 5, .ofs_y = -1}
};

/*---------------------
 *  CHARACTER MAPPING
 *--------------------*/



/*Collect the unicode lists and glyph_id offsets*/
static const lv_font_fmt_txt_cmap_t cmaps[] =
{
    {
        .range_start = 48, .range_length = 10, .glyph_id_start = 1,
        .unicode_list = NULL, .glyph_id_ofs_list = NULL, .list_length = 0, .type = LV_FONT_FMT_TXT_CMAP_FORMAT0_TINY
    }
};



/*--------------------
 *  ALL CUSTOM DATA
 *--------------------*/

#if LVGL_VERSION_MAJOR == 8
/*Store all the custom data of the font*/
static  lv_font_fmt_txt_glyph_cache_t cache;
#endif

#if LVGL_VERSION_MAJOR >= 8
static const lv_font_fmt_txt_dsc_t font_dsc = {
#else
static lv_font_fmt_txt_dsc_t font_dsc = {
#endif
    .glyph_bitmap = glyph_bitmap,
    .glyph_dsc = glyph_dsc,
    .cmaps = cmaps,
    .kern_dsc = NULL,
    .kern_scale = 0,
    .cmap_num = 1,
    .bpp = 4,
    .kern_classes = 0,
    .bitmap_format = 2,
#if LVGL_VERSION_MAJOR == 8
    .cache = &cache
#endif
};



/*-----------------
 *  PUBLIC FONT
 *----------------*/

/*Initialize a public general font descriptor*/
#if LVGL_VERSION_MAJOR >= 8
const lv_font_t hud_font_speed = {
#else
lv_font_t hud_font_speed = {
#endif
    .get_glyph_dsc = lv_font_get_glyph_dsc_fmt_txt,    /*Function pointer to get glyph's data*/
    .get_glyph_bitmap = lv_font_get_bitmap_fmt_txt,    /*Function pointer to get glyph's bitmap*/
    .line_height = 84,          /*The maximum line height required by the font*/
    .base_line = 1,             /*Baseline measured from the bottom of the line*/
#if !(LVGL_VERSION_MAJOR == 6 && LVGL_VERSION_MINOR == 0)
    .subpx = LV_FONT_SUBPX_NONE,
#endif
#if LV_VERSION_CHECK(7, 4, 0) || LVGL_VERSION_MAJOR >= 8
    .underline_position = -12,
    .underline_thickness = 6,
#endif
    .dsc = &font_dsc,          /*The custom font data. Will be accessed by `get_glyph_bitmap/dsc` */
#if LV_VERSION_CHECK(8, 2, 0) || LVGL_VERSION_MAJOR >= 9
    .fallback = NULL,
#endif
    .user_data = NULL,
};



#endif /*#if HUD_FONT_SPEED*/
