WARMW00D/HUD-Audi-A4-B9-MLB-Evo-Waveshare-ESP32-S3-Touch-LCD-3.49/waveshare_hud_mockup/hud_sounds.c

/* Сгенерировано tools/make_sounds.py — не править вручную */
#include "hud_sounds.h"

const int16_t hud_snd_startup[43644] = {
    0, 84, 157, 167, 274, 503, 516, 108, -315, -481, -319, 413, 875, -19, -1107, -1505,
    -1566, -1068, 269, 1311, 1368, 1401, 1907, 1739, -294, -1608, -612, 390, 142, -1265, -2190, -1106,
    463, 802, -371, -2851, -3320, -153, 2211, 2558, 2829, 2687, 447, -2390, -3181, -2980, -2904, -970,
    3521, 4701, 1483, -959, -1111, 1041, 3700, 3165, 365, -907, 560, 3491, 2220, -3427, -5611, -4498,
    -4239, -4718, -2372, 2884, 6254, 6938, 6191, 1965, -4396, -4193, 1107, 3796, 3471, 244, -5400, -8192,
    -6284, -4616, -5854, -7543, -2585, 5911, 7500, 5305, 5511, 8233, 8592, 3296, -2385, -4533, -3619, 1483,
    6543, 2362, -5458, -8522, -8758, -6734, -691, 5285, 6308, 5797, 7139, 7585, 1343, -5353, -3556, 519,
    910, -2604, -6279, -4539, 162, 2118, 169, -5542, -8910, -2868, 4177, 5762, 6064, 6191, 2677, -3551,
    -6316, -5976, -5720, -3442, 4240, 8975, 4537, -711, -2032, 524, 5186, 5976, 1917, -1060, 3, 4287,
    4806, -2675, -7835, -6851, -5816, -6394, -4618, 1799, 7235, 8757, 8242, 4380, -3612, -6215, -513, 3889,
    4308, 1617, -4350, -8877, -7801, -5381, -5759, -7928, -5007, 4049, 8012, 6021, 5260, 7451, 9024, 5132,
    -1006, -4134, -4084, -229, 5802, 4461, -3480, -7984, -8743, -7558, -2627, 4004, 6407, 5867, 6650, 7901,
    3628, -4203, -4797, -541, 1019, -1477, -5655, -5613, -1170, 1792, 944, -3835, -8810, -5249, 2674, 5630,
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
    -6065, 13266, 26455, 28672, 21914, 12154, 3893, -2892, -10839, -20567, -28139, -27463, -15694, 3275, 20701, 28896,
    26269, 17318, 7966, 660, -6359, -15341, -24786, -29160, -23222, -7166, 12256, 25985, 28834, 22438, 12692, 4302,
    -2499, -10326, -20015, -27877, -27801, -16624, 2148, 19908, 28739, 26647, 17884, 8443, 1040, -5917, -14782, -24323,
    -29155, -23866, -8255, 11226, 25478, 28963, 22951, 13235, 4719, -2112, -9819, -19459, -27588, -28100, -17528, 1018,
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
};
const uint32_t hud_snd_swa_beep_len = 4946;
